lab11/blees/software/chips/si7021.c

#include <stdint.h>
#include "nrf_drv_twi.h"
#include <stdbool.h>
#include <math.h>
#include "si7021.h"
#include <string.h>
#include "time.h"

#define Meas_RH_Hold_Master      0xE5  // Measure Relative Humidity, Hold Master Mode
#define Meas_RH_No_Hold_Master   0xF5  // Measure Relative Humidity, No Hold Master Mode
#define Meas_Temp_Hold_Master    0xE3  // Measure Temperature, Hold Master Mode
#define Meas_Temp_No_Hold_Master 0xF3  // Measure Temperature, No Hold Master Mode
#define Read_Temp_From_Prev_RH   0xE0  // Read Temperature Value from Previous RH Measurement
#define RESET                    0xFE  // Reset
#define Write_User_Reg_1         0xE6  // Write RH/T User Register 1
#define Read_User_Reg_1          0xE7  // Read RH/T User Register 1
#define	Read_ID_Byte_1	         0xFA 
#define Read_ID_Byte_1_b         0x0F  // Read 1st Electronic ID
#define Read_ID_Byte_2	         0xFC  // Read 2nd Electronic ID
#define Read_ID_Byte_2_b         0xC9
#define Read_Firm_Rev_1	         0x84  // Read Firmware Revision
#define Read_Firm_Rev_2          0xB8

#define HEATER_ON 	0x04
#define HEATER_OFF  ~(HEATER_ON)

#define TEMP_HUM_ADDR_THIS	0x40

static nrf_drv_twi_t* m_instance;


void si7021_reset () {

	uint8_t data[1] = {RESET};

    nrf_drv_twi_tx(
        m_instance, 
        TEMP_HUM_ADDR_THIS, 
        data,
        sizeof(data),
        false
    );
}

void si7021_init (nrf_drv_twi_t * p_instance) {
	m_instance = p_instance;
}

void si7021_config (si7021_meas_res_t res_mode) {

	uint8_t res1, res0;
	uint8_t reg_status;

	res1 = (res_mode & 0x2) << 6;
	res0 = res_mode & 0x1;

	si7021_read_user_reg(&reg_status);

    uint8_t data[1] = {reg_status | res1 | res0};
    uint8_t command[] = {
    	Write_User_Reg_1,
    	data[0]
    };
    nrf_drv_twi_tx(
        m_instance, 
        TEMP_HUM_ADDR_THIS, 
        command,
        sizeof(command),
        false
    );
}

void si7021_read_temp_hold (float* temp) {

	uint8_t command[] = {Meas_Temp_Hold_Master};

    nrf_drv_twi_tx(
        m_instance, 
        TEMP_HUM_ADDR_THIS, 
        command,
        sizeof(command),
        true
    );
	uint8_t temp_hum_data[3] = {0x00, 0x00, 0x00};
    nrf_drv_twi_rx(
        m_instance, 
        TEMP_HUM_ADDR_THIS, 
        temp_hum_data,
        sizeof(temp_hum_data),
        false
    );

    *temp = -46.85 + (175.72 * (((uint32_t) temp_hum_data[0] << 8) | ((uint32_t) temp_hum_data[1] & 0xfc)) / (1 << 16));
}

void si7021_read_temp (float* temp) {

	uint8_t command[] = {Meas_Temp_No_Hold_Master};
	ret_code_t ret_code;

    nrf_drv_twi_tx(
        m_instance, 
        TEMP_HUM_ADDR_THIS, 
        command,
        sizeof(command),
        true
    );
	uint8_t temp_hum_data[3] = {0, 0, 0};
    do {
    	ret_code =
    	nrf_drv_twi_rx(
        	m_instance, 
        	TEMP_HUM_ADDR_THIS,
            temp_hum_data,
            sizeof(temp_hum_data),
            false
        );
    } while (ret_code != NRF_SUCCESS);

    *temp = -46.85 + (175.72 * (((uint32_t) temp_hum_data[0] << 8) | ((uint32_t) temp_hum_data[1] & 0xfc)) / (1 << 16));
}

static void read_RH (float* hum, uint8_t cmd) {

    uint8_t command[] = {cmd};
    ret_code_t ret_code;

    nrf_drv_twi_tx(
        m_instance, 
        TEMP_HUM_ADDR_THIS, 
        command,
        sizeof(command),
        true
    );
    uint8_t temp_hum_data[3] = {0, 0, 0};
    do {
        ret_code =
        nrf_drv_twi_rx(
            m_instance, 
            TEMP_HUM_ADDR_THIS,
            temp_hum_data,
            sizeof(temp_hum_data),
            false
        );
    } while (ret_code != NRF_SUCCESS);

    *hum = -6.0 + ((125.0 / (1 << 16)) * (((uint32_t) temp_hum_data[0] << 8) | ((uint32_t) temp_hum_data[1] & 0xf0)));
}

void si7021_read_RH_hold (float* hum) {
    read_RH(hum, Meas_RH_Hold_Master);
}

void si7021_read_RH (float* hum) {
    read_RH(hum, Meas_RH_No_Hold_Master);
}


void si7021_read_temp_after_RH (float* temp) {

	uint8_t command[] = {Read_Temp_From_Prev_RH};
    nrf_drv_twi_tx(
        m_instance, 
        TEMP_HUM_ADDR_THIS, 
        command,
        sizeof(command),
        true
    );
	uint8_t temp_hum_data[3] = {0, 0, 0};
    nrf_drv_twi_rx(
        m_instance, 
        TEMP_HUM_ADDR_THIS, 
        temp_hum_data,
        sizeof(temp_hum_data),
        false
    );

    *temp = -46.85 + (175.72 * (((uint32_t) temp_hum_data[0] << 8) | ((uint32_t) temp_hum_data[1] & 0xfc)) / (1 << 16));
}

void si7021_read_temp_and_RH (float* temp, float* hum) {
	si7021_read_RH(hum);
	si7021_read_temp_after_RH(temp); //employ read temp after RH shortcut
}


void si7021_read_user_reg (uint8_t* reg_status) {

	uint8_t command[] = {Read_User_Reg_1};

    nrf_drv_twi_tx(
        m_instance, 
        TEMP_HUM_ADDR_THIS, 
        command,
        sizeof(command),
        true
    );

    nrf_drv_twi_rx(
        m_instance, 
        TEMP_HUM_ADDR_THIS, 
        reg_status,
        sizeof(reg_status),
        false
    );
}

void si7021_read_firmware_rev (uint8_t* buf) {

	uint8_t command[2] = {
		Read_Firm_Rev_1,
		Read_Firm_Rev_2
	};
    nrf_drv_twi_tx(
        m_instance, 
        TEMP_HUM_ADDR_THIS, 
        command,
        sizeof(command),
        true
    );
    nrf_drv_twi_rx(
        m_instance, 
        TEMP_HUM_ADDR_THIS, 
        buf,
        sizeof(buf),
        false
    );
}

void si7021_heater_on () {

	uint8_t reg_status[1] = {0x00};
	si7021_read_user_reg(reg_status);

	uint8_t data[1] = {reg_status[0] | HEATER_ON};
	uint8_t command[] = {
		Write_User_Reg_1,
		data[0]
	};

    nrf_drv_twi_tx(
        m_instance, 
        TEMP_HUM_ADDR_THIS, 
        command,
        sizeof(command),
        false
    );
}

void si7021_heater_off () {

	uint8_t reg_status[1] = {0x00};
	si7021_read_user_reg(reg_status);

	uint8_t data[1] = {reg_status[0] & HEATER_OFF};
	uint8_t command[] =	{
		Write_User_Reg_1,
		data[0]
	};

    nrf_drv_twi_tx(
        m_instance, 
        TEMP_HUM_ADDR_THIS, 
        command,
        sizeof(command),
        false
    );
}
